mattcoates/eviltree/firmware/ChibiOS/os/hal/boards/ST_STM32373C_EVAL/board.h

/*
    ChibiOS - Copyright (C) 2006..2016 Giovanni Di Sirio

    Licensed under the Apache License, Version 2.0 (the "License");
    you may not use this file except in compliance with the License.
    You may obtain a copy of the License at

        http://www.apache.org/licenses/LICENSE-2.0

    Unless required by applicable law or agreed to in writing, software
    distributed under the License is distributed on an "AS IS" BASIS,
    WITHOUT WARRANTIES OR CONDITIONS OF ANY KIND, either express or implied.
    See the License for the specific language governing permissions and
    limitations under the License.
*/

/*
 * This file has been automatically generated using ChibiStudio board
 * generator plugin. Do not edit manually.
 */

#ifndef BOARD_H
#define BOARD_H

/*
 * Setup for STMicroelectronics STM32373C-EVAL board.
 */

/*
 * Board identifier.
 */
#define BOARD_ST_STM32373C_EVAL
#define BOARD_NAME                  "STMicroelectronics STM32373C-EVAL"

/*
 * Board oscillators-related settings.
 */
#if !defined(STM32_LSECLK)
#define STM32_LSECLK                32768U
#endif

#define STM32_LSEDRV                (3U << 3U)

#if !defined(STM32_HSECLK)
#define STM32_HSECLK                8000000U
#endif

/*
 * MCU type as defined in the ST header.
 */
#define STM32F373xC

/*
 * IO pins assignments.
 */
#define GPIOA_WKUP_BUTTON           0U
#define GPIOA_LDR_OUT               1U
#define GPIOA_KEY_BUTTON            2U
#define GPIOA_PIN3                  3U
#define GPIOA_PIN4                  4U
#define GPIOA_PIN5                  5U
#define GPIOA_PIN6                  6U
#define GPIOA_COMP2_OUT             7U
#define GPIOA_I2C2_SMB              8U
#define GPIOA_I2C2_SCL              9U
#define GPIOA_I2C2_SDA              10U
#define GPIOA_USB_DM                11U
#define GPIOA_USB_DP                12U
#define GPIOA_SWDIO                 13U
#define GPIOA_SWCLK                 14U
#define GPIOA_JTDI                  15U

#define GPIOB_MIC_IN                0U
#define GPIOB_ADC_POT_IN            1U
#define GPIOB_PIN2                  2U
#define GPIOB_SWO                   3U
#define GPIOB_JTRST                 4U
#define GPIOB_PIN5                  5U
#define GPIOB_I2C1_SCL              6U
#define GPIOB_I2C1_SDA              7U
#define GPIOB_PIN8                  8U
#define GPIOB_PIN9                  9U
#define GPIOB_PIN10                 10U
#define GPIOB_PIN11                 11U
#define GPIOB_PIN12                 12U
#define GPIOB_PIN13                 13U
#define GPIOB_PIN14                 14U
#define GPIOB_PIN15                 15U

#define GPIOC_LED1                  0U
#define GPIOC_LED2                  1U
#define GPIOC_LED3                  2U
#define GPIOC_LED4                  3U
#define GPIOC_PIN4                  4U
#define GPIOC_USB_DISCONNECT        5U
#define GPIOC_PIN6                  6U
#define GPIOC_PIN7                  7U
#define GPIOC_PIN8                  8U
#define GPIOC_PIN9                  9U
#define GPIOC_SPI3_SCK              10U
#define GPIOC_SPI3_MISO             11U
#define GPIOC_SPI3_MOSI             12U
#define GPIOC_PIN13                 13U
#define GPIOC_OSC32_IN              14U
#define GPIOC_OSC32_OUT             15U

#define GPIOD_CAN_RX                0U
#define GPIOD_CAN_TX                1U
#define GPIOD_LCD_CS                2U
#define GPIOD_USART2_CTS            3U
#define GPIOD_USART2_RST            4U
#define GPIOD_USART2_TX             5U
#define GPIOD_USART2_RX             6U
#define GPIOD_PIN7                  7U
#define GPIOD_PIN8                  8U
#define GPIOD_PIN9                  9U
#define GPIOD_PIN10                 10U
#define GPIOD_AUDIO_RST             11U
#define GPIOD_PIN12                 12U
#define GPIOD_PIN13                 13U
#define GPIOD_PIN14                 14U
#define GPIOD_PIN15                 15U

#define GPIOE_PIN0                  0U
#define GPIOE_PIN1                  1U
#define GPIOE_SD_CS                 2U
#define GPIOE_SD_DETECT             3U
#define GPIOE_PIN4                  4U
#define GPIOE_PIN5                  5U
#define GPIOE_JOY_SEL               6U
#define GPIOE_RTD_IN                7U
#define GPIOE_PRESSUREP             8U
#define GPIOE_PRESSUREN             9U
#define GPIOE_PIN10                 10U
#define GPIOE_PIN11                 11U
#define GPIOE_PIN12                 12U
#define GPIOE_PIN13                 13U
#define GPIOE_PRESSURE_TEPM         14U
#define GPIOE_PIN15                 15U

#define GPIOF_OSC_IN                0U
#define GPIOF_OSC_OUT               1U
#define GPIOF_JOY_DOWN              2U
#define GPIOF_PIN3                  3U
#define GPIOF_JOY_LEFT              4U
#define GPIOF_PIN5                  5U
#define GPIOF_PIN6                  6U
#define GPIOF_PIN7                  7U
#define GPIOF_PIN8                  8U
#define GPIOF_JOY_RIGHT             9U
#define GPIOF_JOY_UP                10U
#define GPIOF_PIN11                 11U
#define GPIOF_PIN12                 12U
#define GPIOF_PIN13                 13U
#define GPIOF_PIN14                 14U
#define GPIOF_PIN15                 15U

#define GPIOG_PIN0                  0U
#define GPIOG_PIN1                  1U
#define GPIOG_PIN2                  2U
#define GPIOG_PIN3                  3U
#define GPIOG_PIN4                  4U
#define GPIOG_PIN5                  5U
#define GPIOG_PIN6                  6U
#define GPIOG_PIN7                  7U
#define GPIOG_PIN8                  8U
#define GPIOG_PIN9                  9U
#define GPIOG_PIN10                 10U
#define GPIOG_PIN11                 11U
#define GPIOG_PIN12                 12U
#define GPIOG_PIN13                 13U
#define GPIOG_PIN14                 14U
#define GPIOG_PIN15                 15U

#define GPIOH_PIN0                  0U
#define GPIOH_PIN1                  1U
#define GPIOH_PIN2                  2U
#define GPIOH_PIN3                  3U
#define GPIOH_PIN4                  4U
#define GPIOH_PIN5                  5U
#define GPIOH_PIN6                  6U
#define GPIOH_PIN7                  7U
#define GPIOH_PIN8                  8U
#define GPIOH_PIN9                  9U
#define GPIOH_PIN10                 10U
#define GPIOH_PIN11                 11U
#define GPIOH_PIN12                 12U
#define GPIOH_PIN13                 13U
#define GPIOH_PIN14                 14U
#define GPIOH_PIN15                 15U

/*
 * IO lines assignments.
 */
#define LINE_WKUP_BUTTON            PAL_LINE(GPIOA, 0U)
#define LINE_LDR_OUT                PAL_LINE(GPIOA, 1U)
#define LINE_KEY_BUTTON             PAL_LINE(GPIOA, 2U)
#define LINE_COMP2_OUT              PAL_LINE(GPIOA, 7U)
#define LINE_I2C2_SMB               PAL_LINE(GPIOA, 8U)
#define LINE_I2C2_SCL               PAL_LINE(GPIOA, 9U)
#define LINE_I2C2_SDA               PAL_LINE(GPIOA, 10U)
#define LINE_USB_DM                 PAL_LINE(GPIOA, 11U)
#define LINE_USB_DP                 PAL_LINE(GPIOA, 12U)
#define LINE_SWDIO                  PAL_LINE(GPIOA, 13U)
#define LINE_SWCLK                  PAL_LINE(GPIOA, 14U)
#define LINE_JTDI                   PAL_LINE(GPIOA, 15U)

#define LINE_MIC_IN                 PAL_LINE(GPIOB, 0U)
#define LINE_ADC_POT_IN             PAL_LINE(GPIOB, 1U)
#define LINE_SWO                    PAL_LINE(GPIOB, 3U)
#define LINE_JTRST                  PAL_LINE(GPIOB, 4U)
#define LINE_I2C1_SCL               PAL_LINE(GPIOB, 6U)
#define LINE_I2C1_SDA               PAL_LINE(GPIOB, 7U)

#define LINE_LED1                   PAL_LINE(GPIOC, 0U)
#define LINE_LED2                   PAL_LINE(GPIOC, 1U)
#define LINE_LED3                   PAL_LINE(GPIOC, 2U)
#define LINE_LED4                   PAL_LINE(GPIOC, 3U)
#define LINE_USB_DISCONNECT         PAL_LINE(GPIOC, 5U)
#define LINE_SPI3_SCK               PAL_LINE(GPIOC, 10U)
#define LINE_SPI3_MISO              PAL_LINE(GPIOC, 11U)
#define LINE_SPI3_MOSI              PAL_LINE(GPIOC, 12U)
#define LINE_OSC32_IN               PAL_LINE(GPIOC, 14U)
#define LINE_OSC32_OUT              PAL_LINE(GPIOC, 15U)

#define LINE_CAN_RX                 PAL_LINE(GPIOD, 0U)
#define LINE_CAN_TX                 PAL_LINE(GPIOD, 1U)
#define LINE_LCD_CS                 PAL_LINE(GPIOD, 2U)
#define LINE_USART2_CTS             PAL_LINE(GPIOD, 3U)
#define LINE_USART2_RST             PAL_LINE(GPIOD, 4U)
#define LINE_USART2_TX              PAL_LINE(GPIOD, 5U)
#define LINE_USART2_RX              PAL_LINE(GPIOD, 6U)
#define LINE_AUDIO_RST              PAL_LINE(GPIOD, 11U)

#define LINE_SD_CS                  PAL_LINE(GPIOE, 2U)
#define LINE_SD_DETECT              PAL_LINE(GPIOE, 3U)
#define LINE_JOY_SEL                PAL_LINE(GPIOE, 6U)
#define LINE_RTD_IN                 PAL_LINE(GPIOE, 7U)
#define LINE_PRESSUREP              PAL_LINE(GPIOE, 8U)
#define LINE_PRESSUREN              PAL_LINE(GPIOE, 9U)
#define LINE_PRESSURE_TEPM          PAL_LINE(GPIOE, 14U)

#define LINE_OSC_IN                 PAL_LINE(GPIOF, 0U)
#define LINE_OSC_OUT                PAL_LINE(GPIOF, 1U)
#define LINE_JOY_DOWN               PAL_LINE(GPIOF, 2U)
#define LINE_JOY_LEFT               PAL_LINE(GPIOF, 4U)
#define LINE_JOY_RIGHT              PAL_LINE(GPIOF, 9U)
#define LINE_JOY_UP                 PAL_LINE(GPIOF, 10U)



/*
 * I/O ports initial setup, this configuration is established soon after reset
 * in the initialization code.
 * Please refer to the STM32 Reference Manual for details.
 */
#define PIN_MODE_INPUT(n)           (0U << ((n) * 2U))
#define PIN_MODE_OUTPUT(n)          (1U << ((n) * 2U))
#define PIN_MODE_ALTERNATE(n)       (2U << ((n) * 2U))
#define PIN_MODE_ANALOG(n)          (3U << ((n) * 2U))
#define PIN_ODR_LOW(n)              (0U << (n))
#define PIN_ODR_HIGH(n)             (1U << (n))
#define PIN_OTYPE_PUSHPULL(n)       (0U << (n))
#define PIN_OTYPE_OPENDRAIN(n)      (1U << (n))
#define PIN_OSPEED_VERYLOW(n)       (0U << ((n) * 2U))
#define PIN_OSPEED_LOW(n)           (1U << ((n) * 2U))
#define PIN_OSPEED_MEDIUM(n)        (2U << ((n) * 2U))
#define PIN_OSPEED_HIGH(n)          (3U << ((n) * 2U))
#define PIN_PUPDR_FLOATING(n)       (0U << ((n) * 2U))
#define PIN_PUPDR_PULLUP(n)         (1U << ((n) * 2U))
#define PIN_PUPDR_PULLDOWN(n)       (2U << ((n) * 2U))
#define PIN_AFIO_AF(n, v)           ((v) << (((n) % 8U) * 4U))

/*
 * GPIOA setup:
 *
 * PA0  - WKUP_BUTTON               (input floating).
 * PA1  - LDR_OUT                   (analog).
 * PA2  - KEY_BUTTON                (input floating).
 * PA3  - PIN3                      (input pullup).
 * PA4  - PIN4                      (input pullup).
 * PA5  - PIN5                      (input floating).
 * PA6  - PIN6                      (input pullup).
 * PA7  - COMP2_OUT                 (output pushpull maximum).
 * PA8  - I2C2_SMB                  (input floating).
 * PA9  - I2C2_SCL                  (alternate 4).
 * PA10 - I2C2_SDA                  (alternate 4).
 * PA11 - USB_DM                    (alternate 14).
 * PA12 - USB_DP                    (alternate 14).
 * PA13 - SWDIO                     (alternate 0).
 * PA14 - SWCLK                     (alternate 0).
 * PA15 - JTDI                      (alternate 0).
 */
#define VAL_GPIOA_MODER             (PIN_MODE_INPUT(GPIOA_WKUP_BUTTON) |    \
                                     PIN_MODE_ANALOG(GPIOA_LDR_OUT) |       \
                                     PIN_MODE_INPUT(GPIOA_KEY_BUTTON) |     \
                                     PIN_MODE_INPUT(GPIOA_PIN3) |           \
                                     PIN_MODE_INPUT(GPIOA_PIN4) |           \
                                     PIN_MODE_INPUT(GPIOA_PIN5) |           \
                                     PIN_MODE_INPUT(GPIOA_PIN6) |           \
                                     PIN_MODE_OUTPUT(GPIOA_COMP2_OUT) |     \
                                     PIN_MODE_INPUT(GPIOA_I2C2_SMB) |       \
                                     PIN_MODE_ALTERNATE(GPIOA_I2C2_SCL) |   \
                                     PIN_MODE_ALTERNATE(GPIOA_I2C2_SDA) |   \
                                     PIN_MODE_ALTERNATE(GPIOA_USB_DM) |     \
                                     PIN_MODE_ALTERNATE(GPIOA_USB_DP) |     \
                                     PIN_MODE_ALTERNATE(GPIOA_SWDIO) |      \
                                     PIN_MODE_ALTERNATE(GPIOA_SWCLK) |      \
                                     PIN_MODE_ALTERNATE(GPIOA_JTDI))
#define VAL_GPIOA_OTYPER            (PIN_OTYPE_PUSHPULL(GPIOA_WKUP_BUTTON) |\
                                     PIN_OTYPE_PUSHPULL(GPIOA_LDR_OUT) |    \
                                     PIN_OTYPE_PUSHPULL(GPIOA_KEY_BUTTON) | \
                                     PIN_OTYPE_PUSHPULL(GPIOA_PIN3) |       \
                                     PIN_OTYPE_PUSHPULL(GPIOA_PIN4) |       \
                                     PIN_OTYPE_PUSHPULL(GPIOA_PIN5) |       \
                                     PIN_OTYPE_PUSHPULL(GPIOA_PIN6) |       \
                                     PIN_OTYPE_PUSHPULL(GPIOA_COMP2_OUT) |  \
                                     PIN_OTYPE_PUSHPULL(GPIOA_I2C2_SMB) |   \
                                     PIN_OTYPE_OPENDRAIN(GPIOA_I2C2_SCL) |  \
                                     PIN_OTYPE_OPENDRAIN(GPIOA_I2C2_SDA) |  \
                                     PIN_OTYPE_PUSHPULL(GPIOA_USB_DM) |     \
                                     PIN_OTYPE_PUSHPULL(GPIOA_USB_DP) |     \
                                     PIN_OTYPE_PUSHPULL(GPIOA_SWDIO) |      \
                                     PIN_OTYPE_PUSHPULL(GPIOA_SWCLK) |      \
                                     PIN_OTYPE_PUSHPULL(GPIOA_JTDI))
#define VAL_GPIOA_OSPEEDR           (PIN_OSPEED_VERYLOW(GPIOA_WKUP_BUTTON) |\
                                     PIN_OSPEED_VERYLOW(GPIOA_LDR_OUT) |    \
                                     PIN_OSPEED_VERYLOW(GPIOA_KEY_BUTTON) | \
                                     PIN_OSPEED_VERYLOW(GPIOA_PIN3) |       \
                                     PIN_OSPEED_VERYLOW(GPIOA_PIN4) |       \
                                     PIN_OSPEED_HIGH(GPIOA_PIN5) |          \
                                     PIN_OSPEED_VERYLOW(GPIOA_PIN6) |       \
                                     PIN_OSPEED_HIGH(GPIOA_COMP2_OUT) |     \
                                     PIN_OSPEED_VERYLOW(GPIOA_I2C2_SMB) |   \
                                     PIN_OSPEED_HIGH(GPIOA_I2C2_SCL) |      \
                                     PIN_OSPEED_HIGH(GPIOA_I2C2_SDA) |      \
                                     PIN_OSPEED_HIGH(GPIOA_USB_DM) |        \
                                     PIN_OSPEED_VERYLOW(GPIOA_USB_DP) |     \
                                     PIN_OSPEED_HIGH(GPIOA_SWDIO) |         \
                                     PIN_OSPEED_HIGH(GPIOA_SWCLK) |         \
                                     PIN_OSPEED_HIGH(GPIOA_JTDI))
#define VAL_GPIOA_PUPDR             (PIN_PUPDR_FLOATING(GPIOA_WKUP_BUTTON) |\
                                     PIN_PUPDR_FLOATING(GPIOA_LDR_OUT) |    \
                                     PIN_PUPDR_FLOATING(GPIOA_KEY_BUTTON) | \
                                     PIN_PUPDR_PULLUP(GPIOA_PIN3) |         \
                                     PIN_PUPDR_PULLUP(GPIOA_PIN4) |         \
                                     PIN_PUPDR_FLOATING(GPIOA_PIN5) |       \
                                     PIN_PUPDR_PULLUP(GPIOA_PIN6) |         \
                                     PIN_PUPDR_FLOATING(GPIOA_COMP2_OUT) |  \
                                     PIN_PUPDR_FLOATING(GPIOA_I2C2_SMB) |   \
                                     PIN_PUPDR_FLOATING(GPIOA_I2C2_SCL) |   \
                                     PIN_PUPDR_FLOATING(GPIOA_I2C2_SDA) |   \
                                     PIN_PUPDR_FLOATING(GPIOA_USB_DM) |     \
                                     PIN_PUPDR_FLOATING(GPIOA_USB_DP) |     \
                                     PIN_PUPDR_PULLUP(GPIOA_SWDIO) |        \
                                     PIN_PUPDR_PULLDOWN(GPIOA_SWCLK) |      \
                                     PIN_PUPDR_FLOATING(GPIOA_JTDI))
#define VAL_GPIOA_ODR               (PIN_ODR_HIGH(GPIOA_WKUP_BUTTON) |      \
                                     PIN_ODR_HIGH(GPIOA_LDR_OUT) |          \
                                     PIN_ODR_HIGH(GPIOA_KEY_BUTTON) |       \
                                     PIN_ODR_HIGH(GPIOA_PIN3) |             \
                                     PIN_ODR_HIGH(GPIOA_PIN4) |             \
                                     PIN_ODR_HIGH(GPIOA_PIN5) |             \
                                     PIN_ODR_HIGH(GPIOA_PIN6) |             \
                                     PIN_ODR_LOW(GPIOA_COMP2_OUT) |         \
                                     PIN_ODR_HIGH(GPIOA_I2C2_SMB) |         \
                                     PIN_ODR_HIGH(GPIOA_I2C2_SCL) |         \
                                     PIN_ODR_HIGH(GPIOA_I2C2_SDA) |         \
                                     PIN_ODR_HIGH(GPIOA_USB_DM) |           \
                                     PIN_ODR_HIGH(GPIOA_USB_DP) |           \
                                     PIN_ODR_HIGH(GPIOA_SWDIO) |            \
                                     PIN_ODR_HIGH(GPIOA_SWCLK) |            \
                                     PIN_ODR_HIGH(GPIOA_JTDI))
#define VAL_GPIOA_AFRL              (PIN_AFIO_AF(GPIOA_WKUP_BUTTON, 0U) |   \
                                     PIN_AFIO_AF(GPIOA_LDR_OUT, 0U) |       \
                                     PIN_AFIO_AF(GPIOA_KEY_BUTTON, 0U) |    \
                                     PIN_AFIO_AF(GPIOA_PIN3, 0U) |          \
                                     PIN_AFIO_AF(GPIOA_PIN4, 0U) |          \
                                     PIN_AFIO_AF(GPIOA_PIN5, 5U) |          \
                                     PIN_AFIO_AF(GPIOA_PIN6, 0U) |          \
                                     PIN_AFIO_AF(GPIOA_COMP2_OUT, 0U))
#define VAL_GPIOA_AFRH              (PIN_AFIO_AF(GPIOA_I2C2_SMB, 0U) |      \
                                     PIN_AFIO_AF(GPIOA_I2C2_SCL, 4U) |      \
                                     PIN_AFIO_AF(GPIOA_I2C2_SDA, 4U) |      \
                                     PIN_AFIO_AF(GPIOA_USB_DM, 14U) |       \
                                     PIN_AFIO_AF(GPIOA_USB_DP, 14U) |       \
                                     PIN_AFIO_AF(GPIOA_SWDIO, 0U) |         \
                                     PIN_AFIO_AF(GPIOA_SWCLK, 0U) |         \
                                     PIN_AFIO_AF(GPIOA_JTDI, 0U))

/*
 * GPIOB setup:
 *
 * PB0  - MIC_IN                    (analog).
 * PB1  - ADC_POT_IN                (analog).
 * PB2  - PIN2                      (input pullup).
 * PB3  - SWO                       (alternate 0).
 * PB4  - JTRST                     (input floating).
 * PB5  - PIN5                      (input pullup).
 * PB6  - I2C1_SCL                  (alternate 4).
 * PB7  - I2C1_SDA                  (alternate 4).
 * PB8  - PIN8                      (input pullup).
 * PB9  - PIN9                      (input pullup).
 * PB10 - PIN10                     (input pullup).
 * PB11 - PIN11                     (input pullup).
 * PB12 - PIN12                     (input pullup).
 * PB13 - PIN13                     (input pullup).
 * PB14 - PIN14                     (input pullup).
 * PB15 - PIN15                     (input pullup).
 */
#define VAL_GPIOB_MODER             (PIN_MODE_ANALOG(GPIOB_MIC_IN) |        \
                                     PIN_MODE_ANALOG(GPIOB_ADC_POT_IN) |    \
                                     PIN_MODE_INPUT(GPIOB_PIN2) |           \
                                     PIN_MODE_ALTERNATE(GPIOB_SWO) |        \
                                     PIN_MODE_INPUT(GPIOB_JTRST) |          \
                                     PIN_MODE_INPUT(GPIOB_PIN5) |           \
                                     PIN_MODE_ALTERNATE(GPIOB_I2C1_SCL) |   \
                                     PIN_MODE_ALTERNATE(GPIOB_I2C1_SDA) |   \
                                     PIN_MODE_INPUT(GPIOB_PIN8) |           \
                                     PIN_MODE_INPUT(GPIOB_PIN9) |           \
                                     PIN_MODE_INPUT(GPIOB_PIN10) |          \
                                     PIN_MODE_INPUT(GPIOB_PIN11) |          \
                                     PIN_MODE_INPUT(GPIOB_PIN12) |          \
                                     PIN_MODE_INPUT(GPIOB_PIN13) |          \
                                     PIN_MODE_INPUT(GPIOB_PIN14) |          \
                                     PIN_MODE_INPUT(GPIOB_PIN15))
#define VAL_GPIOB_OTYPER            (PIN_OTYPE_PUSHPULL(GPIOB_MIC_IN) |     \
                                     PIN_OTYPE_PUSHPULL(GPIOB_ADC_POT_IN) | \
                                     PIN_OTYPE_PUSHPULL(GPIOB_PIN2) |       \
                                     PIN_OTYPE_PUSHPULL(GPIOB_SWO) |        \
                                     PIN_OTYPE_PUSHPULL(GPIOB_JTRST) |      \
                                     PIN_OTYPE_PUSHPULL(GPIOB_PIN5) |       \
                                     PIN_OTYPE_OPENDRAIN(GPIOB_I2C1_SCL) |  \
                                     PIN_OTYPE_OPENDRAIN(GPIOB_I2C1_SDA) |  \
                                     PIN_OTYPE_PUSHPULL(GPIOB_PIN8) |       \
                                     PIN_OTYPE_PUSHPULL(GPIOB_PIN9) |       \
                                     PIN_OTYPE_PUSHPULL(GPIOB_PIN10) |      \
                                     PIN_OTYPE_PUSHPULL(GPIOB_PIN11) |      \
                                     PIN_OTYPE_PUSHPULL(GPIOB_PIN12) |      \
                                     PIN_OTYPE_PUSHPULL(GPIOB_PIN13) |      \
                                     PIN_OTYPE_PUSHPULL(GPIOB_PIN14) |      \
                                     PIN_OTYPE_PUSHPULL(GPIOB_PIN15))
#define VAL_GPIOB_OSPEEDR           (PIN_OSPEED_VERYLOW(GPIOB_MIC_IN) |     \
                                     PIN_OSPEED_VERYLOW(GPIOB_ADC_POT_IN) | \
                                     PIN_OSPEED_VERYLOW(GPIOB_PIN2) |       \
                                     PIN_OSPEED_HIGH(GPIOB_SWO) |           \
                                     PIN_OSPEED_HIGH(GPIOB_JTRST) |         \
                                     PIN_OSPEED_VERYLOW(GPIOB_PIN5) |       \
                                     PIN_OSPEED_HIGH(GPIOB_I2C1_SCL) |      \
                                     PIN_OSPEED_HIGH(GPIOB_I2C1_SDA) |      \
                                     PIN_OSPEED_VERYLOW(GPIOB_PIN8) |       \
                                     PIN_OSPEED_VERYLOW(GPIOB_PIN9) |       \
                                     PIN_OSPEED_VERYLOW(GPIOB_PIN10) |      \
                                     PIN_OSPEED_VERYLOW(GPIOB_PIN11) |      \
                                     PIN_OSPEED_VERYLOW(GPIOB_PIN12) |      \
                                     PIN_OSPEED_VERYLOW(GPIOB_PIN13) |      \
                                     PIN_OSPEED_VERYLOW(GPIOB_PIN14) |      \
                                     PIN_OSPEED_VERYLOW(GPIOB_PIN15))
#define VAL_GPIOB_PUPDR             (PIN_PUPDR_FLOATING(GPIOB_MIC_IN) |     \
                                     PIN_PUPDR_FLOATING(GPIOB_ADC_POT_IN) | \
                                     PIN_PUPDR_PULLUP(GPIOB_PIN2) |         \
                                     PIN_PUPDR_FLOATING(GPIOB_SWO) |        \
                                     PIN_PUPDR_FLOATING(GPIOB_JTRST) |      \
                                     PIN_PUPDR_PULLUP(GPIOB_PIN5) |         \
                                     PIN_PUPDR_FLOATING(GPIOB_I2C1_SCL) |   \
                                     PIN_PUPDR_FLOATING(GPIOB_I2C1_SDA) |   \
                                     PIN_PUPDR_PULLUP(GPIOB_PIN8) |         \
                                     PIN_PUPDR_PULLUP(GPIOB_PIN9) |         \
                                     PIN_PUPDR_PULLUP(GPIOB_PIN10) |        \
                                     PIN_PUPDR_PULLUP(GPIOB_PIN11) |        \
                                     PIN_PUPDR_PULLUP(GPIOB_PIN12) |        \
                                     PIN_PUPDR_PULLUP(GPIOB_PIN13) |        \
                                     PIN_PUPDR_PULLUP(GPIOB_PIN14) |        \
                                     PIN_PUPDR_PULLUP(GPIOB_PIN15))
#define VAL_GPIOB_ODR               (PIN_ODR_HIGH(GPIOB_MIC_IN) |           \
                                     PIN_ODR_HIGH(GPIOB_ADC_POT_IN) |       \
                                     PIN_ODR_HIGH(GPIOB_PIN2) |             \
                                     PIN_ODR_HIGH(GPIOB_SWO) |              \
                                     PIN_ODR_HIGH(GPIOB_JTRST) |            \
                                     PIN_ODR_HIGH(GPIOB_PIN5) |             \
                                     PIN_ODR_HIGH(GPIOB_I2C1_SCL) |         \
                                     PIN_ODR_HIGH(GPIOB_I2C1_SDA) |         \
                                     PIN_ODR_HIGH(GPIOB_PIN8) |             \
                                     PIN_ODR_HIGH(GPIOB_PIN9) |             \
                                     PIN_ODR_HIGH(GPIOB_PIN10) |            \
                                     PIN_ODR_HIGH(GPIOB_PIN11) |            \
                                     PIN_ODR_HIGH(GPIOB_PIN12) |            \
                                     PIN_ODR_HIGH(GPIOB_PIN13) |            \
                                     PIN_ODR_HIGH(GPIOB_PIN14) |            \
                                     PIN_ODR_HIGH(GPIOB_PIN15))
#define VAL_GPIOB_AFRL              (PIN_AFIO_AF(GPIOB_MIC_IN, 0U) |        \
                                     PIN_AFIO_AF(GPIOB_ADC_POT_IN, 0U) |    \
                                     PIN_AFIO_AF(GPIOB_PIN2, 0U) |          \
                                     PIN_AFIO_AF(GPIOB_SWO, 0U) |           \
                                     PIN_AFIO_AF(GPIOB_JTRST, 0U) |         \
                                     PIN_AFIO_AF(GPIOB_PIN5, 0U) |          \
                                     PIN_AFIO_AF(GPIOB_I2C1_SCL, 4U) |      \
                                     PIN_AFIO_AF(GPIOB_I2C1_SDA, 4U))
#define VAL_GPIOB_AFRH              (PIN_AFIO_AF(GPIOB_PIN8, 0U) |          \
                                     PIN_AFIO_AF(GPIOB_PIN9, 0U) |          \
                                     PIN_AFIO_AF(GPIOB_PIN10, 0U) |         \
                                     PIN_AFIO_AF(GPIOB_PIN11, 0U) |         \
                                     PIN_AFIO_AF(GPIOB_PIN12, 0U) |         \
                                     PIN_AFIO_AF(GPIOB_PIN13, 0U) |         \
                                     PIN_AFIO_AF(GPIOB_PIN14, 0U) |         \
                                     PIN_AFIO_AF(GPIOB_PIN15, 0U))

/*
 * GPIOC setup:
 *
 * PC0  - LED1                      (output opendrain maximum).
 * PC1  - LED2                      (output opendrain maximum).
 * PC2  - LED3                      (output opendrain maximum).
 * PC3  - LED4                      (output opendrain maximum).
 * PC4  - PIN4                      (input pullup).
 * PC5  - USB_DISCONNECT            (output pushpull maximum).
 * PC6  - PIN6                      (input pullup).
 * PC7  - PIN7                      (input pullup).
 * PC8  - PIN8                      (input pullup).
 * PC9  - PIN9                      (input pullup).
 * PC10 - SPI3_SCK                  (alternate 6).
 * PC11 - SPI3_MISO                 (alternate 6).
 * PC12 - SPI3_MOSI                 (alternate 6).
 * PC13 - PIN13                     (input pullup).
 * PC14 - OSC32_IN                  (input floating).
 * PC15 - OSC32_OUT                 (input floating).
 */
#define VAL_GPIOC_MODER             (PIN_MODE_OUTPUT(GPIOC_LED1) |          \
                                     PIN_MODE_OUTPUT(GPIOC_LED2) |          \
                                     PIN_MODE_OUTPUT(GPIOC_LED3) |          \
                                     PIN_MODE_OUTPUT(GPIOC_LED4) |          \
                                     PIN_MODE_INPUT(GPIOC_PIN4) |           \
                                     PIN_MODE_OUTPUT(GPIOC_USB_DISCONNECT) |\
                                     PIN_MODE_INPUT(GPIOC_PIN6) |           \
                                     PIN_MODE_INPUT(GPIOC_PIN7) |           \
                                     PIN_MODE_INPUT(GPIOC_PIN8) |           \
                                     PIN_MODE_INPUT(GPIOC_PIN9) |           \
                                     PIN_MODE_ALTERNATE(GPIOC_SPI3_SCK) |   \
                                     PIN_MODE_ALTERNATE(GPIOC_SPI3_MISO) |  \
                                     PIN_MODE_ALTERNATE(GPIOC_SPI3_MOSI) |  \
                                     PIN_MODE_INPUT(GPIOC_PIN13) |          \
                                     PIN_MODE_INPUT(GPIOC_OSC32_IN) |       \
                                     PIN_MODE_INPUT(GPIOC_OSC32_OUT))
#define VAL_GPIOC_OTYPER            (PIN_OTYPE_OPENDRAIN(GPIOC_LED1) |      \
                                     PIN_OTYPE_OPENDRAIN(GPIOC_LED2) |      \
                                     PIN_OTYPE_OPENDRAIN(GPIOC_LED3) |      \
                                     PIN_OTYPE_OPENDRAIN(GPIOC_LED4) |      \
                                     PIN_OTYPE_PUSHPULL(GPIOC_PIN4) |       \
                                     PIN_OTYPE_PUSHPULL(GPIOC_USB_DISCONNECT) |\
                                     PIN_OTYPE_PUSHPULL(GPIOC_PIN6) |       \
                                     PIN_OTYPE_PUSHPULL(GPIOC_PIN7) |       \
                                     PIN_OTYPE_PUSHPULL(GPIOC_PIN8) |       \
                                     PIN_OTYPE_PUSHPULL(GPIOC_PIN9) |       \
                                     PIN_OTYPE_PUSHPULL(GPIOC_SPI3_SCK) |   \
                                     PIN_OTYPE_PUSHPULL(GPIOC_SPI3_MISO) |  \
                                     PIN_OTYPE_PUSHPULL(GPIOC_SPI3_MOSI) |  \
                                     PIN_OTYPE_PUSHPULL(GPIOC_PIN13) |      \
                                     PIN_OTYPE_PUSHPULL(GPIOC_OSC32_IN) |   \
                                     PIN_OTYPE_PUSHPULL(GPIOC_OSC32_OUT))
#define VAL_GPIOC_OSPEEDR           (PIN_OSPEED_HIGH(GPIOC_LED1) |          \
                                     PIN_OSPEED_HIGH(GPIOC_LED2) |          \
                                     PIN_OSPEED_HIGH(GPIOC_LED3) |          \
                                     PIN_OSPEED_HIGH(GPIOC_LED4) |          \
                                     PIN_OSPEED_VERYLOW(GPIOC_PIN4) |       \
                                     PIN_OSPEED_HIGH(GPIOC_USB_DISCONNECT) |\
                                     PIN_OSPEED_VERYLOW(GPIOC_PIN6) |       \
                                     PIN_OSPEED_VERYLOW(GPIOC_PIN7) |       \
                                     PIN_OSPEED_VERYLOW(GPIOC_PIN8) |       \
                                     PIN_OSPEED_VERYLOW(GPIOC_PIN9) |       \
                                     PIN_OSPEED_HIGH(GPIOC_SPI3_SCK) |      \
                                     PIN_OSPEED_HIGH(GPIOC_SPI3_MISO) |     \
                                     PIN_OSPEED_HIGH(GPIOC_SPI3_MOSI) |     \
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
                                     PIN_AFIO_AF(GPIOC_PIN13, 0U) |         \
                                     PIN_AFIO_AF(GPIOC_OSC32_IN, 0U) |      \
                                     PIN_AFIO_AF(GPIOC_OSC32_OUT, 0U))

/*
 * GPIOD setup:
 *
 * PD0  - CAN_RX                    (alternate 7).
 * PD1  - CAN_TX                    (alternate 7).
 * PD2  - LCD_CS                    (output pushpull maximum).
 * PD3  - USART2_CTS                (alternate 7).
 * PD4  - USART2_RST                (alternate 7).
 * PD5  - USART2_TX                 (alternate 7).
 * PD6  - USART2_RX                 (alternate 7).
 * PD7  - PIN7                      (input pullup).
 * PD8  - PIN8                      (input pullup).
 * PD9  - PIN9                      (input pullup).
 * PD10 - PIN10                     (input pullup).
 * PD11 - AUDIO_RST                 (output pushpull maximum).
 * PD12 - PIN12                     (input pullup).
 * PD13 - PIN13                     (input pullup).
 * PD14 - PIN14                     (input pullup).
 * PD15 - PIN15                     (input pullup).
 */
#define VAL_GPIOD_MODER             (PIN_MODE_ALTERNATE(GPIOD_CAN_RX) |     \
                                     PIN_MODE_ALTERNATE(GPIOD_CAN_TX) |     \
                                     PIN_MODE_OUTPUT(GPIOD_LCD_CS) |        \
                                     PIN_MODE_ALTERNATE(GPIOD_USART2_CTS) | \
                                     PIN_MODE_ALTERNATE(GPIOD_USART2_RST) | \
                                     PIN_MODE_ALTERNATE(GPIOD_USART2_TX) |  \
                                     PIN_MODE_ALTERNATE(GPIOD_USART2_RX) |  \
                                     PIN_MODE_INPUT(GPIOD_PIN7) |           \
                                     PIN_MODE_INPUT(GPIOD_PIN8) |           \
                                     PIN_MODE_INPUT(GPIOD_PIN9) |           \
                                     PIN_MODE_INPUT(GPIOD_PIN10) |          \
                                     PIN_MODE_OUTPUT(GPIOD_AUDIO_RST) |     \
                                     PIN_MODE_INPUT(GPIOD_PIN12) |          \
                                     PIN_MODE_INPUT(GPIOD_PIN13) |          \
                                     PIN_MODE_INPUT(GPIOD_PIN14) |          \
                                     PIN_MODE_INPUT(GPIOD_PIN15))
#define VAL_GPIOD_OTYPER            (PIN_OTYPE_PUSHPULL(GPIOD_CAN_RX) |     \
                                     PIN_OTYPE_PUSHPULL(GPIOD_CAN_TX) |     \
                                     PIN_OTYPE_PUSHPULL(GPIOD_LCD_CS) |     \
                                     PIN_OTYPE_PUSHPULL(GPIOD_USART2_CTS) | \
                                     PIN_OTYPE_PUSHPULL(GPIOD_USART2_RST) | \
                                     PIN_OTYPE_PUSHPULL(GPIOD_USART2_TX) |  \
                                     PIN_OTYPE_PUSHPULL(GPIOD_USART2_RX) |  \
                                     PIN_OTYPE_PUSHPULL(GPIOD_PIN7) |       \
                                     PIN_OTYPE_PUSHPULL(GPIOD_PIN8) |       \
                                     PIN_OTYPE_PUSHPULL(GPIOD_PIN9) |       \
                                     PIN_OTYPE_PUSHPULL(GPIOD_PIN10) |      \
                                     PIN_OTYPE_PUSHPULL(GPIOD_AUDIO_RST) |  \
                                     PIN_OTYPE_PUSHPULL(GPIOD_PIN12) |      \
                                     PIN_OTYPE_PUSHPULL(GPIOD_PIN13) |      \
                                     PIN_OTYPE_PUSHPULL(GPIOD_PIN14) |      \
                                     PIN_OTYPE_PUSHPULL(GPIOD_PIN15))
#define VAL_GPIOD_OSPEEDR           (PIN_OSPEED_HIGH(GPIOD_CAN_RX) |        \
                                     PIN_OSPEED_HIGH(GPIOD_CAN_TX) |        \
                                     PIN_OSPEED_HIGH(GPIOD_LCD_CS) |        \
                                     PIN_OSPEED_HIGH(GPIOD_USART2_CTS) |    \
                                     PIN_OSPEED_HIGH(GPIOD_USART2_RST) |    \
                                     PIN_OSPEED_HIGH(GPIOD_USART2_TX) |     \
                                     PIN_OSPEED_HIGH(GPIOD_USART2_RX) |     \
                                     PIN_OSPEED_VERYLOW(GPIOD_PIN7) |       \
                                     PIN_OSPEED_VERYLOW(GPIOD_PIN8) |       \
                                     PIN_OSPEED_VERYLOW(GPIOD_PIN9) |       \
                                     PIN_OSPEED_VERYLOW(GPIOD_PIN10) |      \
                                     PIN_OSPEED_HIGH(GPIOD_AUDIO_RST) |     \
                                     PIN_OSPEED_VERYLOW(GPIOD_PIN12) |      \
                                     PIN_OSPEED_VERYLOW(GPIOD_PIN13) |      \
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
                                     PIN_AFIO_AF(GPIOD_PIN13, 0U) |         \
                                     PIN_AFIO_AF(GPIOD_PIN14, 0U) |         \
                                     PIN_AFIO_AF(GPIOD_PIN15, 0U))

/*
 * GPIOE setup:
 *
 * PE0  - PIN0                      (input pullup).
 * PE1  - PIN1                      (input pullup).
 * PE2  - SD_CS                     (output opendrain maximum).
 * PE3  - SD_DETECT                 (input pullup).
 * PE4  - PIN4                      (input pullup).
 * PE5  - PIN5                      (input pullup).
 * PE6  - JOY_SEL                   (input pulldown).
 * PE7  - RTD_IN                    (analog).
 * PE8  - PRESSUREP                 (analog).
 * PE9  - PRESSUREN                 (analog).
 * PE10 - PIN10                     (input pullup).
 * PE11 - PIN11                     (input pullup).
 * PE12 - PIN12                     (input pullup).
 * PE13 - PIN13                     (input pullup).
 * PE14 - PRESSURE_TEPM             (input floating).
 * PE15 - PIN15                     (input pullup).
 */
#define VAL_GPIOE_MODER             (PIN_MODE_INPUT(GPIOE_PIN0) |           \
                                     PIN_MODE_INPUT(GPIOE_PIN1) |           \
                                     PIN_MODE_OUTPUT(GPIOE_SD_CS) |         \
                                     PIN_MODE_INPUT(GPIOE_SD_DETECT) |      \
                                     PIN_MODE_INPUT(GPIOE_PIN4) |           \
                                     PIN_MODE_INPUT(GPIOE_PIN5) |           \
                                     PIN_MODE_INPUT(GPIOE_JOY_SEL) |        \
                                     PIN_MODE_ANALOG(GPIOE_RTD_IN) |        \
                                     PIN_MODE_ANALOG(GPIOE_PRESSUREP) |     \
                                     PIN_MODE_ANALOG(GPIOE_PRESSUREN) |     \
                                     PIN_MODE_INPUT(GPIOE_PIN10) |          \
                                     PIN_MODE_INPUT(GPIOE_PIN11) |          \
                                     PIN_MODE_INPUT(GPIOE_PIN12) |          \
                                     PIN_MODE_INPUT(GPIOE_PIN13) |          \
                                     PIN_MODE_INPUT(GPIOE_PRESSURE_TEPM) |  \
                                     PIN_MODE_INPUT(GPIOE_PIN15))
#define VAL_GPIOE_OTYPER            (PIN_OTYPE_PUSHPULL(GPIOE_PIN0) |       \
                                     PIN_OTYPE_PUSHPULL(GPIOE_PIN1) |       \
                                     PIN_OTYPE_OPENDRAIN(GPIOE_SD_CS) |     \
                                     PIN_OTYPE_PUSHPULL(GPIOE_SD_DETECT) |  \
                                     PIN_OTYPE_PUSHPULL(GPIOE_PIN4) |       \
                                     PIN_OTYPE_PUSHPULL(GPIOE_PIN5) |       \
                                     PIN_OTYPE_PUSHPULL(GPIOE_JOY_SEL) |    \
                                     PIN_OTYPE_PUSHPULL(GPIOE_RTD_IN) |     \
                                     PIN_OTYPE_PUSHPULL(GPIOE_PRESSUREP) |  \
                                     PIN_OTYPE_PUSHPULL(GPIOE_PRESSUREN) |  \
                                     PIN_OTYPE_PUSHPULL(GPIOE_PIN10) |      \
                                     PIN_OTYPE_PUSHPULL(GPIOE_PIN11) |      \
                                     PIN_OTYPE_PUSHPULL(GPIOE_PIN12) |      \
                                     PIN_OTYPE_PUSHPULL(GPIOE_PIN13) |      \
                                     PIN_OTYPE_PUSHPULL(GPIOE_PRESSURE_TEPM) |\
                                     PIN_OTYPE_PUSHPULL(GPIOE_PIN15))
#define VAL_GPIOE_OSPEEDR           (PIN_OSPEED_VERYLOW(GPIOE_PIN0) |       \
                                     PIN_OSPEED_VERYLOW(GPIOE_PIN1) |       \
                                     PIN_OSPEED_HIGH(GPIOE_SD_CS) |         \
                                     PIN_OSPEED_HIGH(GPIOE_SD_DETECT) |     \
                                     PIN_OSPEED_VERYLOW(GPIOE_PIN4) |       \
                                     PIN_OSPEED_VERYLOW(GPIOE_PIN5) |       \
                                     PIN_OSPEED_HIGH(GPIOE_JOY_SEL) |       \
                                     PIN_OSPEED_VERYLOW(GPIOE_RTD_IN) |     \
                                     PIN_OSPEED_HIGH(GPIOE_PRESSUREP) |     \
                                     PIN_OSPEED_HIGH(GPIOE_PRESSUREN) |     \
                                     PIN_OSPEED_VERYLOW(GPIOE_PIN10) |      \
                                     PIN_OSPEED_VERYLOW(GPIOE_PIN11) |      \
                                     PIN_OSPEED_VERYLOW(GPIOE_PIN12) |      \
                                     PIN_OSPEED_VERYLOW(GPIOE_PIN13) |      \
                                     PIN_OSPEED_VERYLOW(GPIOE_PRESSURE_TEPM) |\
                                     PIN_OSPEED_VERYLOW(GPIOE_PIN15))
#define VAL_GPIOE_PUPDR             (PIN_PUPDR_PULLUP(GPIOE_PIN0) |         \
                                     PIN_PUPDR_PULLUP(GPIOE_PIN1) |         \
                                     PIN_PUPDR_FLOATING(GPIOE_SD_CS) |      \
                                     PIN_PUPDR_PULLUP(GPIOE_SD_DETECT) |    \
                                     PIN_PUPDR_PULLUP(GPIOE_PIN4) |         \
                                     PIN_PUPDR_PULLUP(GPIOE_PIN5) |         \
                                     PIN_PUPDR_PULLDOWN(GPIOE_JOY_SEL) |    \
                                     PIN_PUPDR_FLOATING(GPIOE_RTD_IN) |     \
                                     PIN_PUPDR_FLOATING(GPIOE_PRESSUREP) |  \
                                     PIN_PUPDR_FLOATING(GPIOE_PRESSUREN) |  \
                                     PIN_PUPDR_PULLUP(GPIOE_PIN10) |        \
                                     PIN_PUPDR_PULLUP(GPIOE_PIN11) |        \
                                     PIN_PUPDR_PULLUP(GPIOE_PIN12) |        \
                                     PIN_PUPDR_PULLUP(GPIOE_PIN13) |        \
                                     PIN_PUPDR_FLOATING(GPIOE_PRESSURE_TEPM) |\
                                     PIN_PUPDR_PULLUP(GPIOE_PIN15))
#define VAL_GPIOE_ODR               (PIN_ODR_HIGH(GPIOE_PIN0) |             \
                                     PIN_ODR_HIGH(GPIOE_PIN1) |             \
                                     PIN_ODR_HIGH(GPIOE_SD_CS) |            \
                                     PIN_ODR_HIGH(GPIOE_SD_DETECT) |        \
                                     PIN_ODR_HIGH(GPIOE_PIN4) |             \
                                     PIN_ODR_HIGH(GPIOE_PIN5) |             \
                                     PIN_ODR_HIGH(GPIOE_JOY_SEL) |          \
                                     PIN_ODR_HIGH(GPIOE_RTD_IN) |           \
                                     PIN_ODR_HIGH(GPIOE_PRESSUREP) |        \
                                     PIN_ODR_HIGH(GPIOE_PRESSUREN) |        \
                                     PIN_ODR_HIGH(GPIOE_PIN10) |            \
                                     PIN_ODR_HIGH(GPIOE_PIN11) |            \
                                     PIN_ODR_HIGH(GPIOE_PIN12) |            \
                                     PIN_ODR_LOW(GPIOE_PIN13) |             \
                                     PIN_ODR_LOW(GPIOE_PRESSURE_TEPM) |     \
                                     PIN_ODR_LOW(GPIOE_PIN15))
#define VAL_GPIOE_AFRL              (PIN_AFIO_AF(GPIOE_PIN0, 0U) |          \
                                     PIN_AFIO_AF(GPIOE_PIN1, 0U) |          \
                                     PIN_AFIO_AF(GPIOE_SD_CS, 0U) |         \
                                     PIN_AFIO_AF(GPIOE_SD_DETECT, 0U) |     \
                                     PIN_AFIO_AF(GPIOE_PIN4, 0U) |          \
                                     PIN_AFIO_AF(GPIOE_PIN5, 0U) |          \
                                     PIN_AFIO_AF(GPIOE_JOY_SEL, 0U) |       \
                                     PIN_AFIO_AF(GPIOE_RTD_IN, 0U))
#define VAL_GPIOE_AFRH              (PIN_AFIO_AF(GPIOE_PRESSUREP, 0U) |     \
                                     PIN_AFIO_AF(GPIOE_PRESSUREN, 0U) |     \
                                     PIN_AFIO_AF(GPIOE_PIN10, 0U) |         \
                                     PIN_AFIO_AF(GPIOE_PIN11, 0U) |         \
                                     PIN_AFIO_AF(GPIOE_PIN12, 0U) |         \
                                     PIN_AFIO_AF(GPIOE_PIN13, 0U) |         \
                                     PIN_AFIO_AF(GPIOE_PRESSURE_TEPM, 0U) | \
                                     PIN_AFIO_AF(GPIOE_PIN15, 0U))

/*
 * GPIOF setup:
 *
 * PF0  - OSC_IN                    (input floating).
 * PF1  - OSC_OUT                   (input floating).
 * PF2  - JOY_DOWN                  (input pulldown).
 * PF3  - PIN3                      (input pullup).
 * PF4  - JOY_LEFT                  (input pulldown).
 * PF5  - PIN5                      (input pullup).
 * PF6  - PIN6                      (input pullup).
 * PF7  - PIN7                      (input pullup).
 * PF8  - PIN8                      (input pullup).
 * PF9  - JOY_RIGHT                 (input pulldown).
 * PF10 - JOY_UP                    (input pulldown).
 * PF11 - PIN11                     (input pullup).
 * PF12 - PIN12                     (input pullup).
 * PF13 - PIN13                     (input pullup).
 * PF14 - PIN14                     (input pullup).
 * PF15 - PIN15                     (input pullup).
 */
#define VAL_GPIOF_MODER             (PIN_MODE_INPUT(GPIOF_OSC_IN) |         \
                                     PIN_MODE_INPUT(GPIOF_OSC_OUT) |        \
                                     PIN_MODE_INPUT(GPIOF_JOY_DOWN) |       \
                                     PIN_MODE_INPUT(GPIOF_PIN3) |           \
                                     PIN_MODE_INPUT(GPIOF_JOY_LEFT) |       \
                                     PIN_MODE_INPUT(GPIOF_PIN5) |           \
                                     PIN_MODE_INPUT(GPIOF_PIN6) |           \
                                     PIN_MODE_INPUT(GPIOF_PIN7) |           \
                                     PIN_MODE_INPUT(GPIOF_PIN8) |           \
                                     PIN_MODE_INPUT(GPIOF_JOY_RIGHT) |      \
                                     PIN_MODE_INPUT(GPIOF_JOY_UP) |         \
                                     PIN_MODE_INPUT(GPIOF_PIN11) |          \
                                     PIN_MODE_INPUT(GPIOF_PIN12) |          \
                                     PIN_MODE_INPUT(GPIOF_PIN13) |          \
                                     PIN_MODE_INPUT(GPIOF_PIN14) |          \
                                     PIN_MODE_INPUT(GPIOF_PIN15))
#define VAL_GPIOF_OTYPER            (PIN_OTYPE_PUSHPULL(GPIOF_OSC_IN) |     \
                                     PIN_OTYPE_PUSHPULL(GPIOF_OSC_OUT) |    \
                                     PIN_OTYPE_PUSHPULL(GPIOF_JOY_DOWN) |   \
                                     PIN_OTYPE_PUSHPULL(GPIOF_PIN3) |       \
                                     PIN_OTYPE_PUSHPULL(GPIOF_JOY_LEFT) |   \
                                     PIN_OTYPE_PUSHPULL(GPIOF_PIN5) |       \
                                     PIN_OTYPE_PUSHPULL(GPIOF_PIN6) |       \
                                     PIN_OTYPE_PUSHPULL(GPIOF_PIN7) |       \
                                     PIN_OTYPE_PUSHPULL(GPIOF_PIN8) |       \
                                     PIN_OTYPE_PUSHPULL(GPIOF_JOY_RIGHT) |  \
                                     PIN_OTYPE_PUSHPULL(GPIOF_JOY_UP) |     \
                                     PIN_OTYPE_PUSHPULL(GPIOF_PIN11) |      \
                                     PIN_OTYPE_PUSHPULL(GPIOF_PIN12) |      \
                                     PIN_OTYPE_PUSHPULL(GPIOF_PIN13) |      \
                                     PIN_OTYPE_PUSHPULL(GPIOF_PIN14) |      \
                                     PIN_OTYPE_PUSHPULL(GPIOF_PIN15))
#define VAL_GPIOF_OSPEEDR           (PIN_OSPEED_HIGH(GPIOF_OSC_IN) |        \
                                     PIN_OSPEED_HIGH(GPIOF_OSC_OUT) |       \
                                     PIN_OSPEED_HIGH(GPIOF_JOY_DOWN) |      \
                                     PIN_OSPEED_VERYLOW(GPIOF_PIN3) |       \
                                     PIN_OSPEED_HIGH(GPIOF_JOY_LEFT) |      \
                                     PIN_OSPEED_VERYLOW(GPIOF_PIN5) |       \
                                     PIN_OSPEED_VERYLOW(GPIOF_PIN6) |       \
                                     PIN_OSPEED_VERYLOW(GPIOF_PIN7) |       \
                                     PIN_OSPEED_VERYLOW(GPIOF_PIN8) |       \
                                     PIN_OSPEED_HIGH(GPIOF_JOY_RIGHT) |     \
                                     PIN_OSPEED_HIGH(GPIOF_JOY_UP) |        \
                                     PIN_OSPEED_VERYLOW(GPIOF_PIN11) |      \
                                     PIN_OSPEED_VERYLOW(GPIOF_PIN12) |      \
                                     PIN_OSPEED_VERYLOW(GPIOF_PIN13) |      \
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
                                     PIN_PUPDR_PULLUP(GPIOH_PIN14) |        \
                                     PIN_PUPDR_PULLUP(GPIOH_PIN15))
#define VAL_GPIOH_ODR               (PIN_ODR_HIGH(GPIOH_PIN0) |             \
                                     PIN_ODR_HIGH(GPIOH_PIN1) |             \
                                     PIN_ODR_HIGH(GPIOH_PIN2) |             \
                                     PIN_ODR_HIGH(GPIOH_PIN3) |             \
                                     PIN_ODR_HIGH(GPIOH_PIN4) |             \
                                     PIN_ODR_HIGH(GPIOH_PIN5) |             \
                                     PIN_ODR_HIGH(GPIOH_PIN6) |             \
                                     PIN_ODR_HIGH(GPIOH_PIN7) |             \
                                     PIN_ODR_HIGH(GPIOH_PIN8) |             \
                                     PIN_ODR_HIGH(GPIOH_PIN9) |             \
                                     PIN_ODR_HIGH(GPIOH_PIN10) |            \
                                     PIN_ODR_HIGH(GPIOH_PIN11) |            \
                                     PIN_ODR_HIGH(GPIOH_PIN12) |            \
                                     PIN_ODR_HIGH(GPIOH_PIN13) |            \
                                     PIN_ODR_HIGH(GPIOH_PIN14) |            \
                                     PIN_ODR_HIGH(GPIOH_PIN15))
#define VAL_GPIOH_AFRL              (PIN_AFIO_AF(GPIOH_PIN0, 0U) |          \
                                     PIN_AFIO_AF(GPIOH_PIN1, 0U) |          \
                                     PIN_AFIO_AF(GPIOH_PIN2, 0U) |          \
                                     PIN_AFIO_AF(GPIOH_PIN3, 0U) |          \
                                     PIN_AFIO_AF(GPIOH_PIN4, 0U) |          \
                                     PIN_AFIO_AF(GPIOH_PIN5, 0U) |          \
                                     PIN_AFIO_AF(GPIOH_PIN6, 0U) |          \
                                     PIN_AFIO_AF(GPIOH_PIN7, 0U))
#define VAL_GPIOH_AFRH              (PIN_AFIO_AF(GPIOH_PIN8, 0U) |          \
                                     PIN_AFIO_AF(GPIOH_PIN9, 0U) |          \
                                     PIN_AFIO_AF(GPIOH_PIN10, 0U) |         \
                                     PIN_AFIO_AF(GPIOH_PIN11, 0U) |         \
                                     PIN_AFIO_AF(GPIOH_PIN12, 0U) |         \
                                     PIN_AFIO_AF(GPIOH_PIN13, 0U) |         \
                                     PIN_AFIO_AF(GPIOH_PIN14, 0U) |         \
                                     PIN_AFIO_AF(GPIOH_PIN15, 0U))


#if !defined(_FROM_ASM_)
#ifdef __cplusplus
extern "C" {
#endif
  void boardInit(void);
#ifdef __cplusplus
}
#endif
#endif /* _FROM_ASM_ */

#endif /* BOARD_H */
